alvarop/nui/fw/nui/hw/bsp/nui_v1p0/include/bsp/bsp.h

/*
 * Licensed to the Apache Software Foundation (ASF) under one
 * or more contributor license agreements.  See the NOTICE file
 * distributed with this work for additional information
 * regarding copyright ownership.  The ASF licenses this file
 * to you under the Apache License, Version 2.0 (the
 * "License"); you may not use this file except in compliance
 * with the License.  You may obtain a copy of the License at
 *
 *  http://www.apache.org/licenses/LICENSE-2.0
 *
 * Unless required by applicable law or agreed to in writing,
 * software distributed under the License is distributed on an
 * "AS IS" BASIS, WITHOUT WARRANTIES OR CONDITIONS OF ANY
 * KIND, either express or implied.  See the License for the
 * specific language governing permissions and limitations
 * under the License.
 */

#ifndef H_BSP_H
#define H_BSP_H

#include <inttypes.h>

#include <syscfg/syscfg.h>

#ifdef __cplusplus
extern "C" {
#endif

/* Define special stackos sections */
#define sec_data_core   __attribute__((section(".data.core")))
#define sec_bss_core    __attribute__((section(".bss.core")))
#define sec_bss_nz_core __attribute__((section(".bss.core.nz")))

/* More convenient section placement macros. */
#define bssnz_t         sec_bss_nz_core

extern uint8_t _ram_start;
#define RAM_SIZE        0x10000

#define MUTE_N_PIN 0
#define MISO_PIN 1
#define SCK_PIN 4
#define MOSI_PIN 6
#define CS_N_PIN 9
#define ZC_EN_PIN 10
#define IR_IN_PIN 25

#define LED_BLINK_PIN 30

#ifdef __cplusplus
}
#endif

#endif  /* H_BSP_H */
